ZhekaiJin/UAV-Charging/Totem Project Zhekai Jin/realization 2/Board 2.JPG

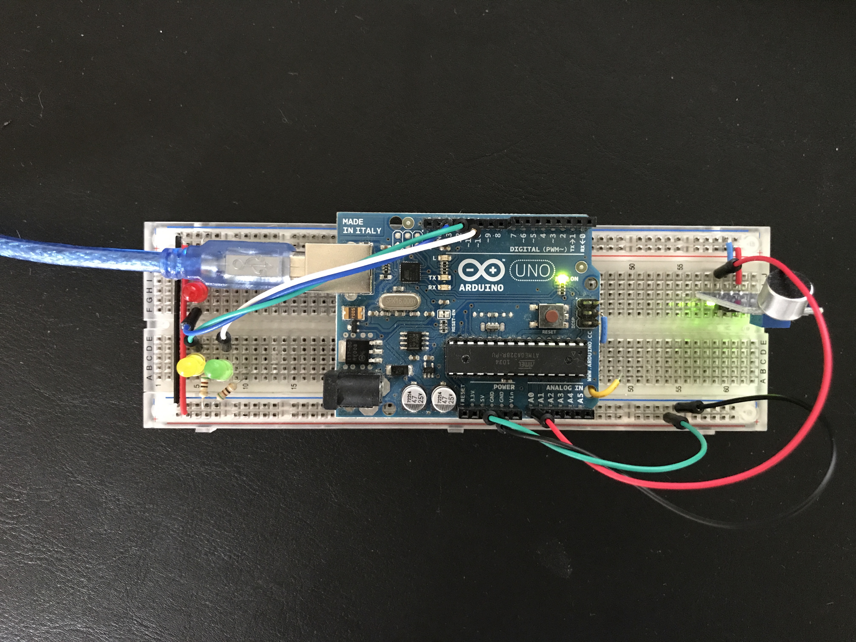
Totem Project Zhekai Jin/realization 2/Board 2.JPG
