ZhekaiJin/UAV-Charging/Totem Project Zhekai Jin/realization 1/board diagram.JPG

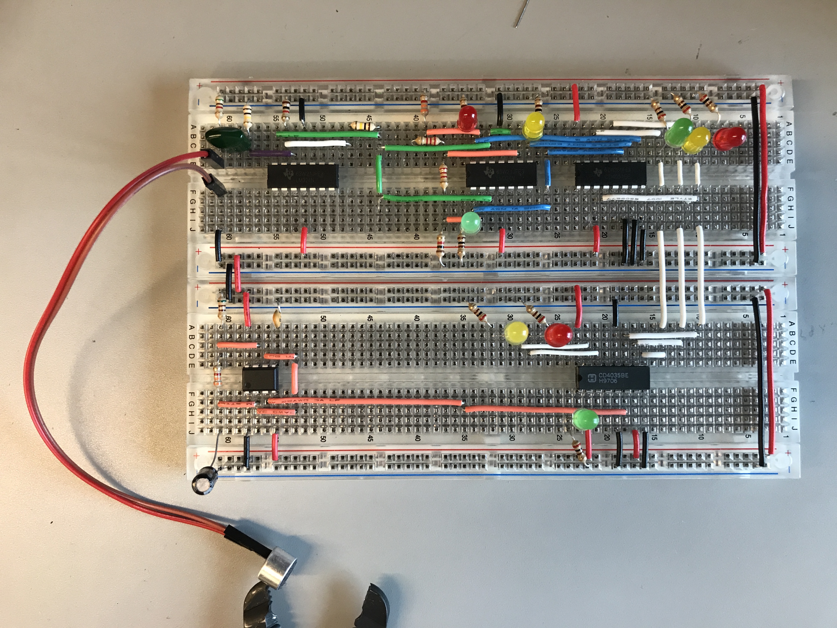
Totem Project Zhekai Jin/realization 1/board diagram.JPG
