ZhekaiJin/UAV-Charging/doc/FSK-Demodulation-Circuit.png

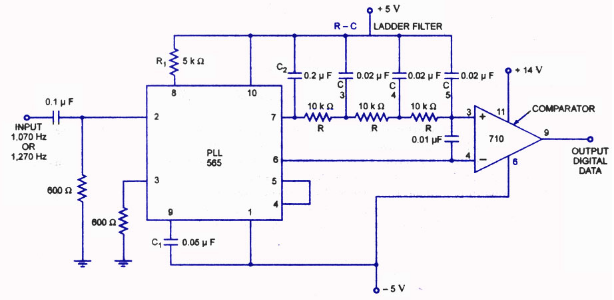
doc/FSK-Demodulation-Circuit.png
