ZhekaiJin/UAV-Charging/doc/FSK-Modulation-Circuit-Using-555-Timer.png

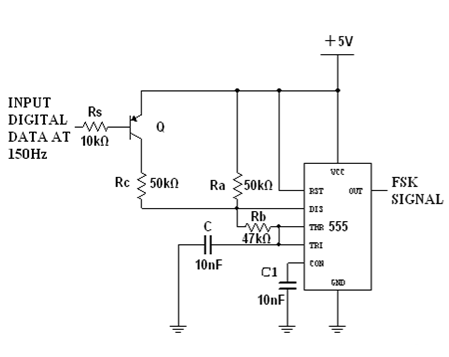
doc/FSK-Modulation-Circuit-Using-555-Timer.png
