ZhekaiJin/UAV-Charging/TEST DATA/OVERVIEW.png

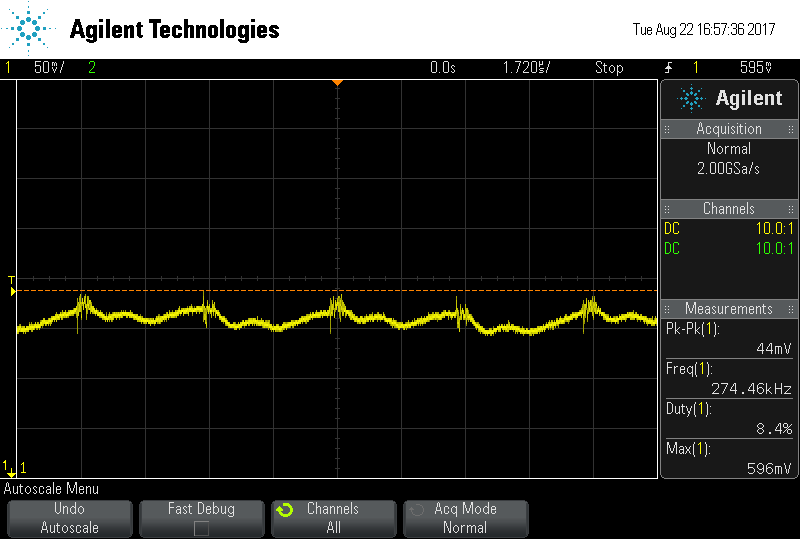
TEST DATA/OVERVIEW.png
