ZhekaiJin/UAV-Charging/Totem Project Zhekai Jin/realization 1/schematic 1.bmp

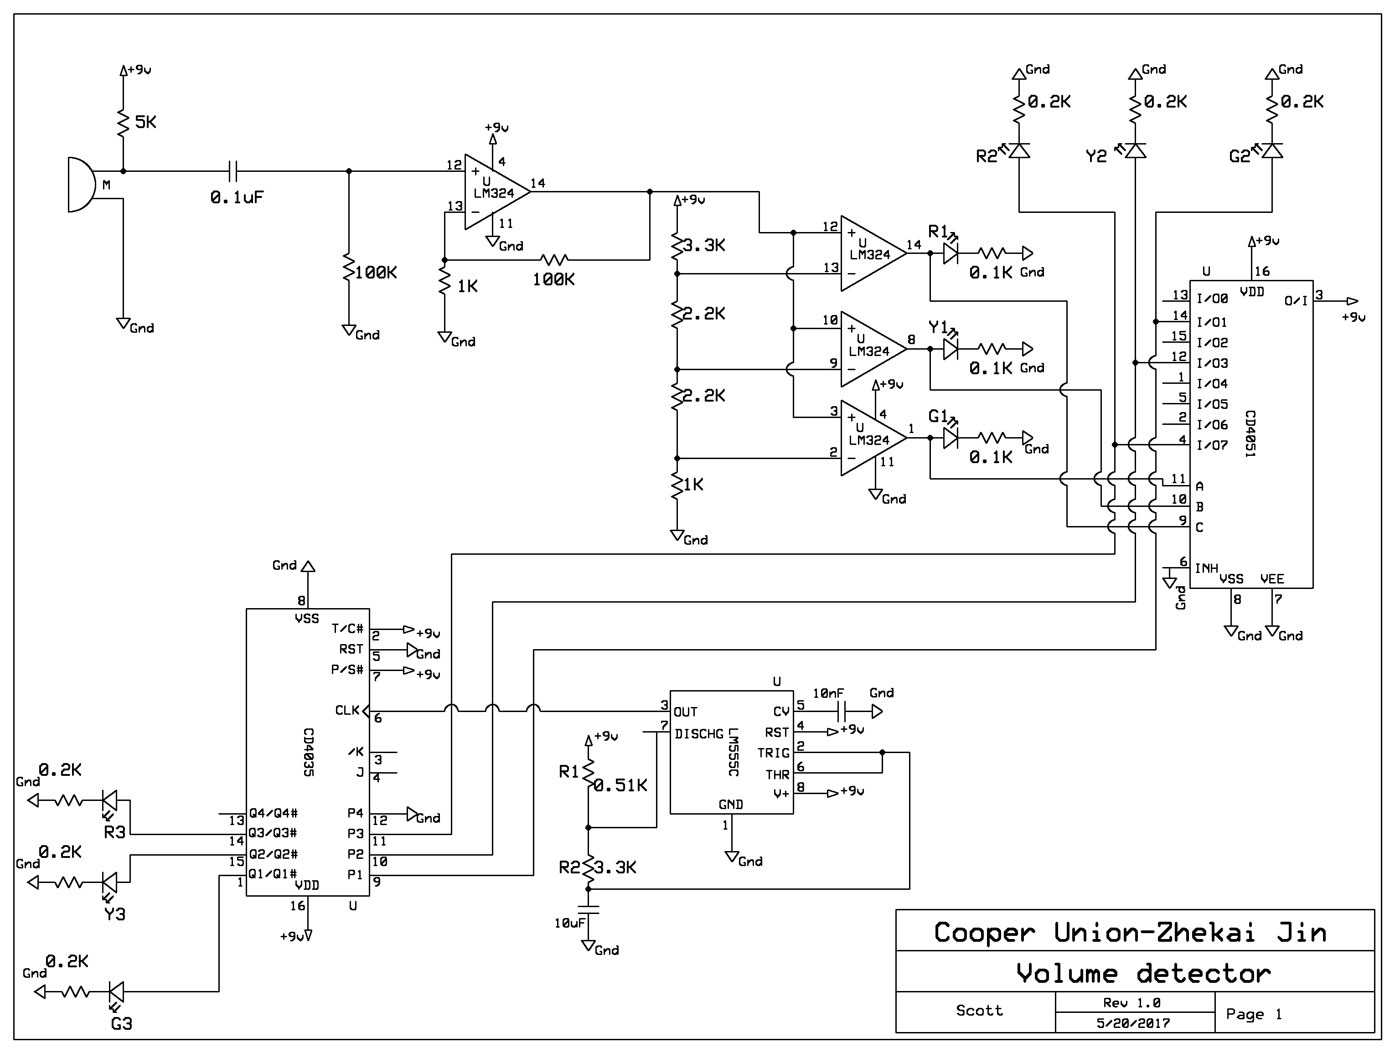
Totem Project Zhekai Jin/realization 1/schematic 1.bmp
