ZhekaiJin/UAV-Charging/TEST DATA/ISNS PING.csv

x-axis | 1
second | Volt
-780.0000E-03 | +20.4774E-03
-779.2200E-03 | +25.0000E-03
-778.4400E-03 | +29.0201E-03
-777.6600E-03 | +20.4774E-03
-776.8800E-03 | +20.4774E-03
-776.1000E-03 | +20.4774E-03
-775.3200E-03 | +20.4774E-03
-774.5400E-03 | +16.9598E-03
-773.7600E-03 | +12.4372E-03
-772.9800E-03 | +4.3970E-03
-772.2000E-03 | +4.3970E-03
-771.4200E-03 | -3.6432E-03
-770.6400E-03 | -11.6834E-03
-769.8600E-03 | -27.7638E-03
-769.0800E-03 | -19.7236E-03
-768.3000E-03 | -19.7236E-03
-767.5200E-03 | -19.7236E-03
-766.7400E-03 | -11.6834E-03
-765.9600E-03 | -3.6432E-03
-765.1800E-03 | +4.3970E-03
-764.4000E-03 | +4.3970E-03
-763.6200E-03 | +12.4372E-03
-762.8400E-03 | +20.4774E-03
-762.0600E-03 | +16.4573E-03
-761.2800E-03 | +28.5176E-03
-760.5000E-03 | +20.4774E-03
-759.7200E-03 | +20.4774E-03
-758.9400E-03 | +20.4774E-03
-758.1600E-03 | +12.4372E-03
-757.3800E-03 | +12.4372E-03
-756.6000E-03 | +12.4372E-03
-755.8200E-03 | +8.9196E-03
-755.0400E-03 | -19.7236E-03
-754.2600E-03 | -31.2814E-03
-753.4800E-03 | -43.3417E-03
-752.7000E-03 | -31.2814E-03
-751.9200E-03 | -27.2613E-03
-751.1400E-03 | -27.7638E-03
-750.3600E-03 | -19.7236E-03
-749.5800E-03 | -3.6432E-03
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
