ZhekaiJin/UAV-Charging/TEST DATA/OUT VS OUTS.csv

x-axis | 1 | 2
second | Volt | Volt
-500.0000E-03 | +3.6180904E+00 | +4.8994974E+00
-499.5000E-03 | +3.6984924E+00 | +4.8241206E+00
-499.0000E-03 | +3.6180904E+00 | +4.8241206E+00
-498.5000E-03 | +3.6532663E+00 | +4.8592964E+00
-498.0000E-03 | +3.6180904E+00 | +4.8241206E+00
-497.5000E-03 | +3.7336683E+00 | +4.8592964E+00
-497.0000E-03 | +3.6984924E+00 | +4.9045226E+00
-496.5000E-03 | +3.6934673E+00 | +4.8592964E+00
-496.0000E-03 | +3.6180904E+00 | +4.8241206E+00
-495.5000E-03 | +3.7336683E+00 | +4.8241206E+00
-495.0000E-03 | +3.6984924E+00 | +4.9045226E+00
-494.5000E-03 | +3.6582914E+00 | +4.8643216E+00
-494.0000E-03 | +3.7738693E+00 | +4.9045226E+00
-493.5000E-03 | +3.6984924E+00 | +4.8643216E+00
-493.0000E-03 | +3.6180904E+00 | +4.8994974E+00
-492.5000E-03 | +3.7788944E+00 | +4.9045226E+00
-492.0000E-03 | +3.6934673E+00 | +4.9045226E+00
-491.5000E-03 | +3.6984924E+00 | +4.9447236E+00
-491.0000E-03 | +3.8542713E+00 | +4.8241206E+00
-490.5000E-03 | +3.7336683E+00 | +4.9045226E+00
-490.0000E-03 | +3.6180904E+00 | +4.8241206E+00
-489.5000E-03 | +3.6984924E+00 | +4.9045226E+00
-489.0000E-03 | +3.5376884E+00 | +4.8241206E+00
-488.5000E-03 | +3.6582914E+00 | +4.8643216E+00
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
