ZhekaiJin/UAV-Charging/TEST DATA/RECT VS OUT.csv

x-axis | 1 | 2
second | Volt | Volt
-500.0000E-03 | +7.0753768E+00 | +4.9045226E+00
-499.5000E-03 | +7.0301507E+00 | +4.8241206E+00
-499.0000E-03 | +7.2311557E+00 | +4.8994974E+00
-498.5000E-03 | +7.3115577E+00 | +4.9045226E+00
-498.0000E-03 | +7.3115577E+00 | +4.9045226E+00
-497.5000E-03 | +6.1909547E+00 | +4.9045226E+00
-497.0000E-03 | +5.8693467E+00 | +4.8994974E+00
-496.5000E-03 | +5.8693467E+00 | +4.8592964E+00
-496.0000E-03 | +7.2311557E+00 | +4.9045226E+00
-495.5000E-03 | +5.7889447E+00 | +4.8643216E+00
-495.0000E-03 | +6.9949748E+00 | +4.9045226E+00
-494.5000E-03 | +5.8241205E+00 | +4.8643216E+00
-494.0000E-03 | +7.1557788E+00 | +4.9045226E+00
-493.5000E-03 | +5.9497487E+00 | +4.8592964E+00
-493.0000E-03 | +5.7085427E+00 | +4.8241206E+00
-492.5000E-03 | +5.8693467E+00 | +4.9447236E+00
-492.0000E-03 | +7.1557788E+00 | +4.9045226E+00
-491.5000E-03 | +6.1507537E+00 | +4.8592964E+00
-491.0000E-03 | +5.8693467E+00 | +4.9045226E+00
-490.5000E-03 | +5.9095477E+00 | +4.9045226E+00
-490.0000E-03 | +5.9497487E+00 | +4.8994974E+00
-489.5000E-03 | +7.3567838E+00 | +4.9045226E+00
-489.0000E-03 | +5.9447236E+00 | +4.8994974E+00
-488.5000E-03 | +7.2763818E+00 | +4.9045226E+00
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
