ZhekaiJin/UAV-Charging/TEST DATA/VSNS  LPM.csv

x-axis | 1
second | Volt
-499.8500E-03 | -201.0050E-03
-499.3500E-03 | -201.0050E-03
-498.8500E-03 | -178.3920E-03
-498.3500E-03 | -201.0050E-03
-497.8500E-03 | -178.3920E-03
-497.3500E-03 | -178.3920E-03
-496.8500E-03 | -180.9045E-03
-496.3500E-03 | -201.0050E-03
-495.8500E-03 | -180.9045E-03
-495.3500E-03 | -160.8040E-03
-494.8500E-03 | -178.3920E-03
-494.3500E-03 | -160.8040E-03
-493.8500E-03 | -201.0050E-03
-493.3500E-03 | -201.0050E-03
-492.8500E-03 | -201.0050E-03
-492.3500E-03 | -180.9045E-03
-491.8500E-03 | -180.9045E-03
-491.3500E-03 | -201.0050E-03
-490.8500E-03 | -201.0050E-03
-490.3500E-03 | -178.3920E-03
-489.8500E-03 | -201.0050E-03
-489.3500E-03 | -201.0050E-03
-488.8500E-03 | -201.0050E-03
-488.3500E-03 | -201.0050E-03
-487.8500E-03 | -201.0050E-03
-487.3500E-03 | -201.0050E-03
-486.8500E-03 | -201.0050E-03
-486.3500E-03 | -201.0050E-03
-485.8500E-03 | -201.0050E-03
-485.3500E-03 | -201.0050E-03
-484.8500E-03 | -201.0050E-03
-484.3500E-03 | -201.0050E-03
-483.8500E-03 | -178.3920E-03
-483.3500E-03 | -178.3920E-03
-482.8500E-03 | -180.9045E-03
-482.3500E-03 | -180.9045E-03
-481.8500E-03 | -178.3920E-03
-481.3500E-03 | -180.9045E-03
-480.8500E-03 | -180.9045E-03
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
