ZhekaiJin/UAV-Charging/TEST DATA/ISNS PING.png

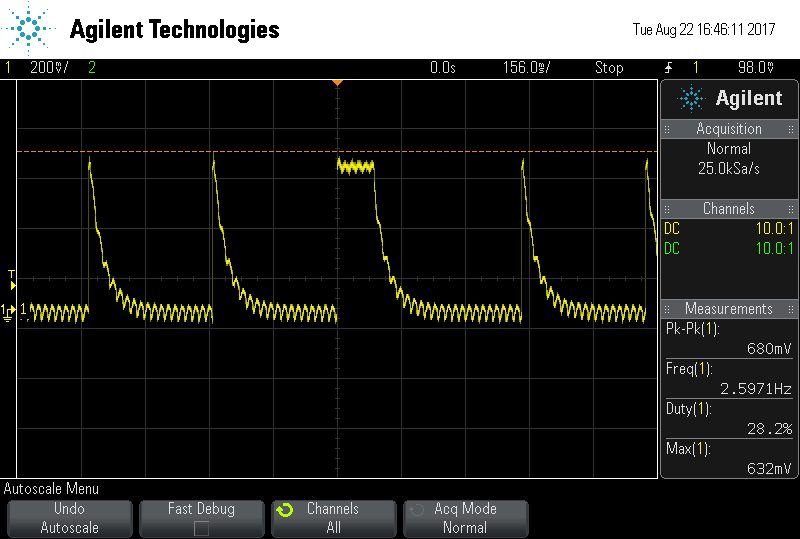
TEST DATA/ISNS PING.png
