ZhekaiJin/UAV-Charging/TEST DATA/PACKAGE (ISNS).png

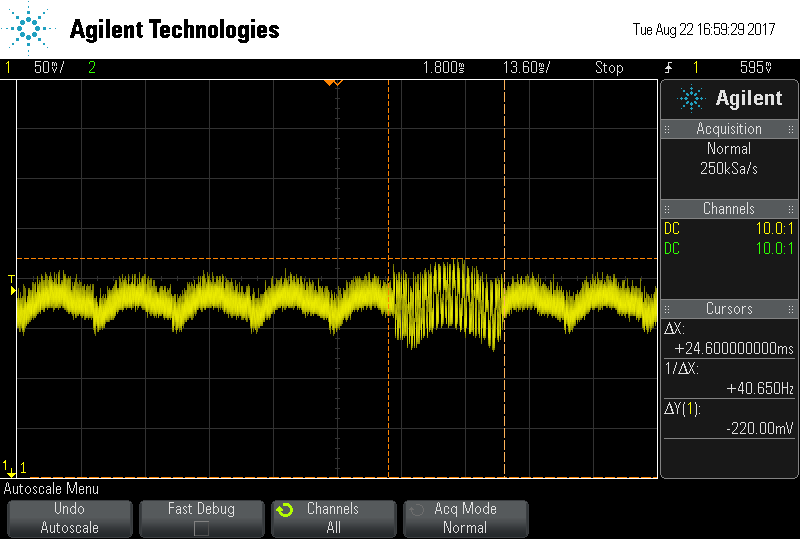
TEST DATA/PACKAGE (ISNS).png
