ZhekaiJin/UAV-Charging/TEST DATA/scope_13.png

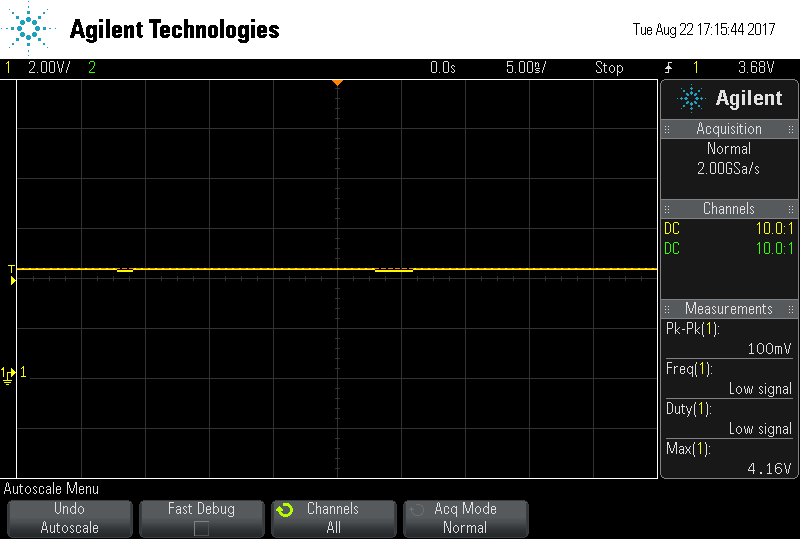
TEST DATA/scope_13.png
