ZhekaiJin/UAV-Charging/TEST DATA/VOUT ON BABYSITTER.png

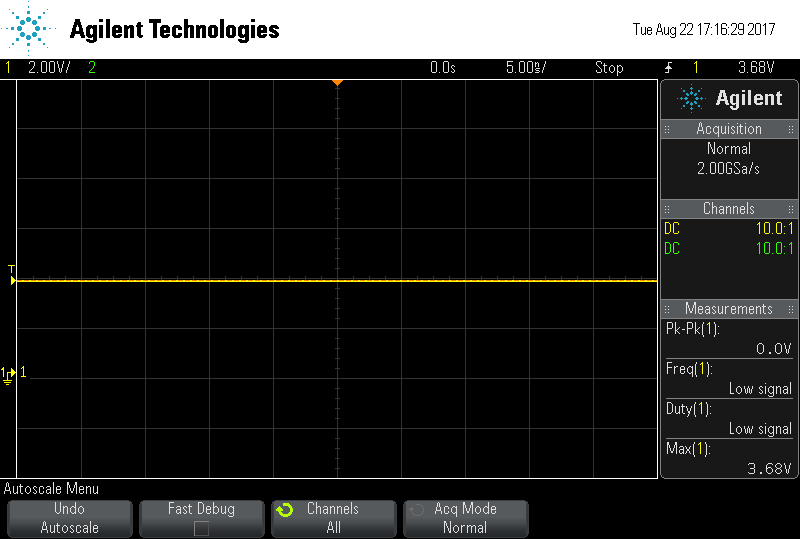
TEST DATA/VOUT ON BABYSITTER.png
