ZhekaiJin/UAV-Charging/TEST DATA/VSNS  LPM.png

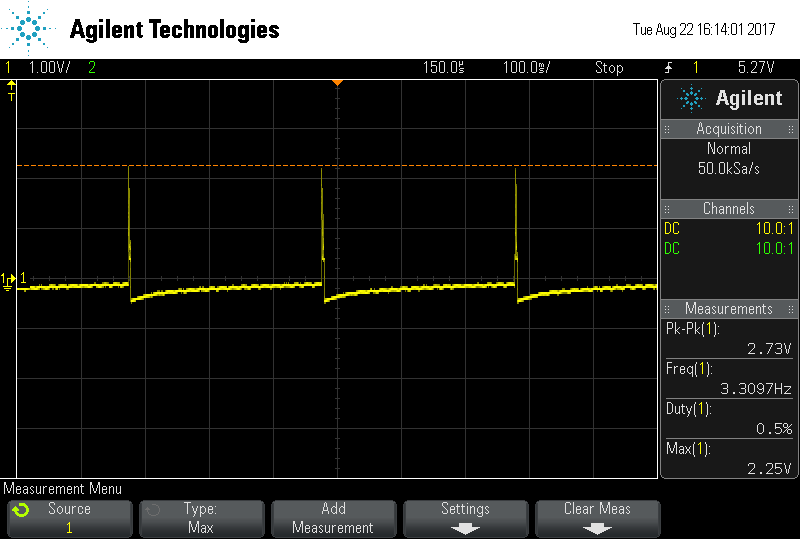
TEST DATA/VSNS LPM.png
