ZhekaiJin/UAV-Charging/TEST DATA/VSNS &ISNS @.png

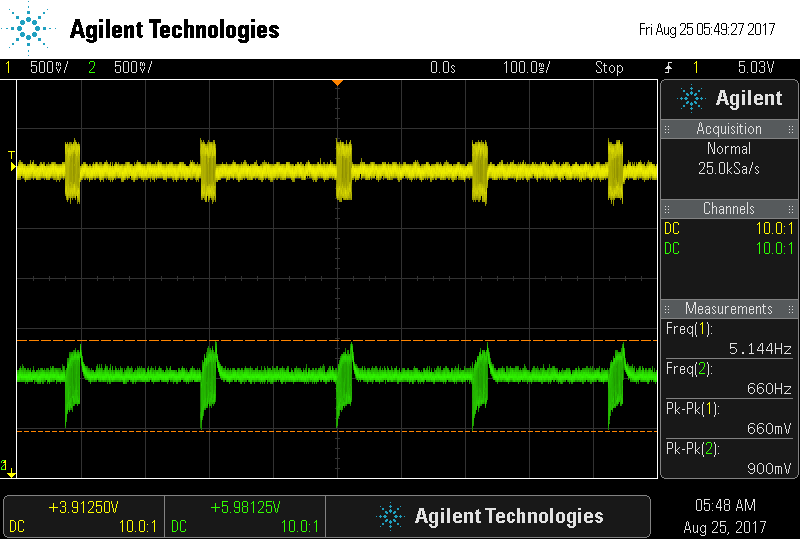
TEST DATA/VSNS &ISNS @.png
